ElektorLabs/200478-Touchless-Lightswitch/firmware/Firmware/src/config.h

//This will enable debug information foe OTA over serial
#define DEBUG_SERIAL_OTA 

//This will enable debug informaton for the webserver over serial
#define DEBUG_SERIAL

//Debug infos for WiFI
#define DEBUG_SERIAL_WIFI

//Debug Infos for the Datastore
#define DEBUG_SERIAL_DATASTORE

 #define DEBUG_SERIAL_WWW     
