ElektorLabs/200478-Touchless-Lightswitch/firmware/Firmware/src/datastore.h

#ifndef DATASTORE_H_
 #define DATASTORE_H_
 
 
typedef struct {
  char ssid[128];
  char pass[128];
} credentials_t;
/* 256 byte */

typedef struct{
  bool WIFI_Ena;
  char ap_pass[128];
  bool AP_Enc_Ena;
  bool AP_Mode;
  bool NoFallbackToAP;
} wifi_param_config_t;

/**************************************************************************************************
 *    Function      : datastoresetup
 *    Description   : Gets the EEPROM Emulation set up
 *    Input         : none 
 *    Output        : none
 *    Remarks       : We use 4096 byte for EEPROM 
 **************************************************************************************************/
void datastoresetup();

/**************************************************************************************************
 *    Function      : write_wifi_config
 *    Description   : writes the wifi config
 *    Input         : wifi_param_config_t c 
 *    Output        : none
 *    Remarks       : none 
 **************************************************************************************************/
void write_wifi_config(wifi_param_config_t c);


/**************************************************************************************************
 *    Function      : read_wifi_config
 *    Description   : writes the wifi config
 *    Input         : none
 *    Output        : wifi_param_config_t
 *    Remarks       : none
 **************************************************************************************************/
wifi_param_config_t read_wifi_config( void );


/**************************************************************************************************
 *    Function      : write_credentials
 *    Description   : writes the wifi credentials
 *    Input         : credentials_t
 *    Output        : none
 *    Remarks       : none
 **************************************************************************************************/
void write_credentials(credentials_t c);


/**************************************************************************************************
 *    Function      : read_credentials
 *    Description   : reads the wifi credentials
 *    Input         : none
 *    Output        : credentials_t
 *    Remarks       : none
 **************************************************************************************************/
credentials_t read_credentials( void );

/**************************************************************************************************
 *    Function      : datastore_erase
 *    Description   : deletes the datastore 
 *    Input         : none
 *    Output        : none
 *    Remarks       : This will invalidate all user data 
 **************************************************************************************************/
void datastore_erase( void );


#endif
