ElektorLabs/200478-Touchless-Lightswitch/firmware/Firmware/src/driver/touchinput.h

#ifndef __TOUCHINPUT_H__
 #define __TOUCHINPUT_H__

#include <Arduino.h>

#include <flick.h>
#include <stdio.h>
#include <unistd.h>


void TouchInput_begin( uint8_t xferPin, uint8_t resetPin );
   
#endif
